JeramayaGramby/AnalogStateBuckConverter/cad/step/BLOCK_10/SMF5_0A.step

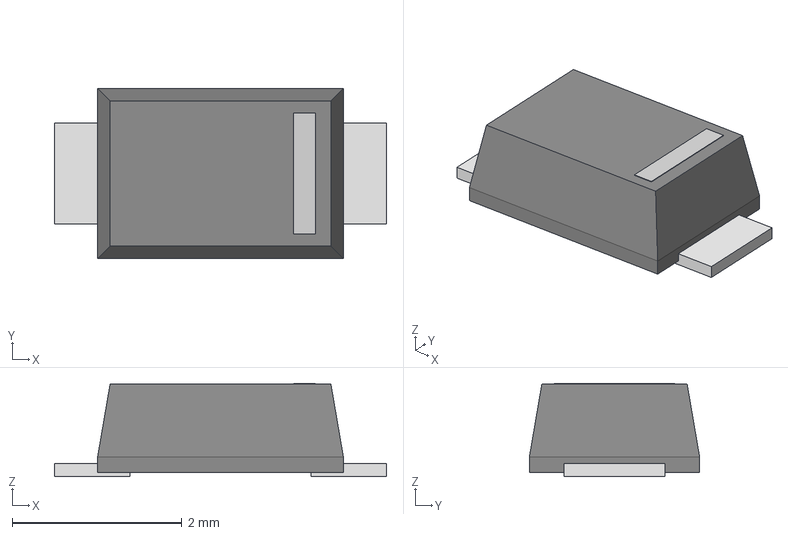
[picture p15: CAD file, 2026-02-01]
cad/step/BLOCK_10/SMF5_0A.step
3.91 x 2.01 x 1.10 mm
