JeramayaGramby/AnalogStateBuckConverter/cad/step/BLOCK_3/NPNTRANSISTOR.step

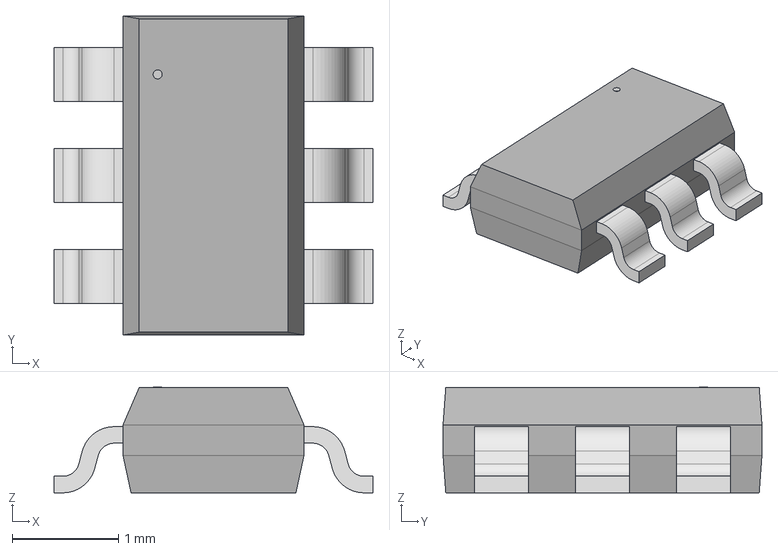
[picture p16: CAD file, 2026-01-31]
cad/step/BLOCK_3/NPNTRANSISTOR.step
3.00 x 3.00 x 0.993 mm
