JeramayaGramby/AnalogStateBuckConverter/cad/step/BLOCK_4/TNPV1206330KBYEA.step

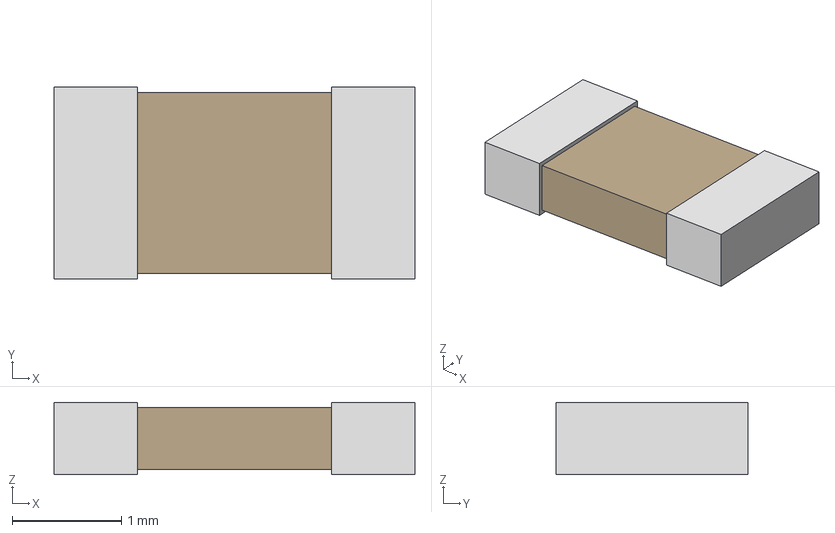
[picture p17: CAD file, 2026-01-31]
cad/step/BLOCK_4/TNPV1206330KBYEA.step
3.30 x 1.75 x 0.66 mm
