JeramayaGramby/AnalogStateBuckConverter/cad/step/BLOCK_5/CRCW040256K2FKED.STEP

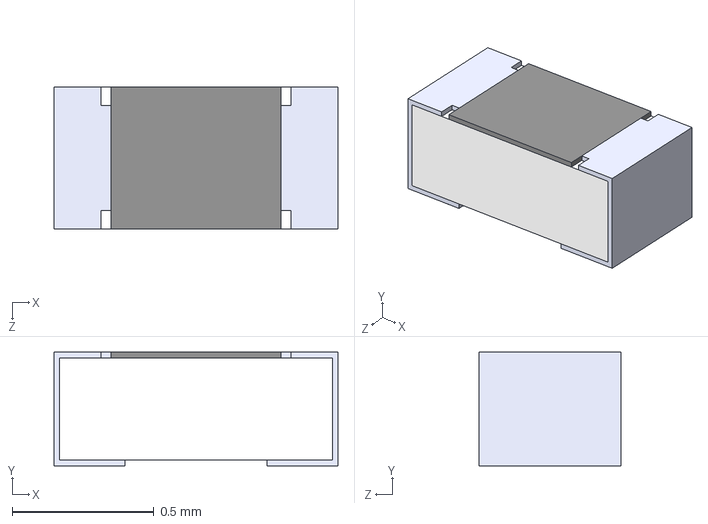
[picture p18: CAD file, 2026-01-31]
cad/step/BLOCK_5/CRCW040256K2FKED.STEP
1 x 0.4 x 0.5 mm
