JeramayaGramby/AnalogStateBuckConverter/cad/step/BLOCK_6/600S100JT250XT4K.step

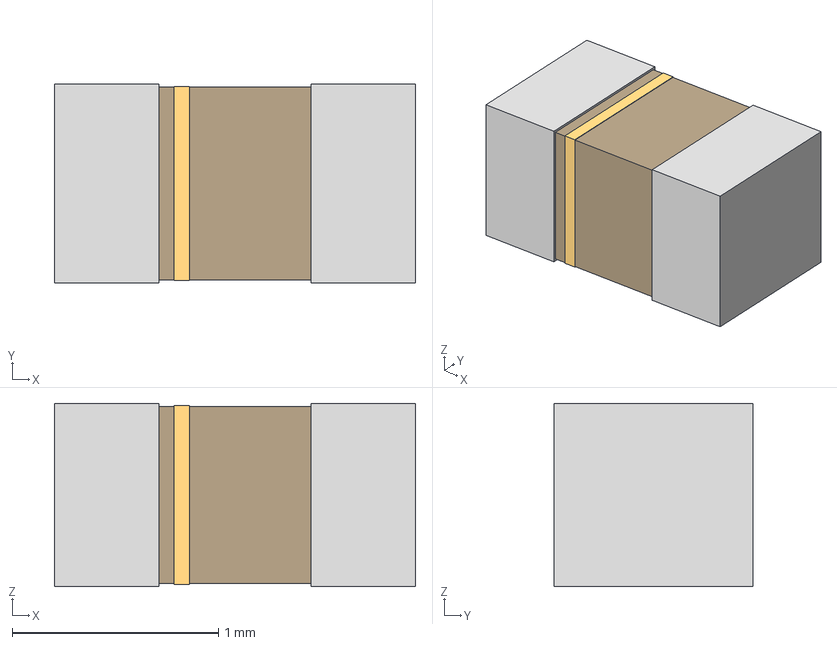
[picture p19: CAD file, 2026-01-31]
cad/step/BLOCK_6/600S100JT250XT4K.step
1.75 x 0.966 x 0.889 mm
