JeramayaGramby/AnalogStateBuckConverter/cad/step/BLOCK_7/CRCW06031K20FKEA.step

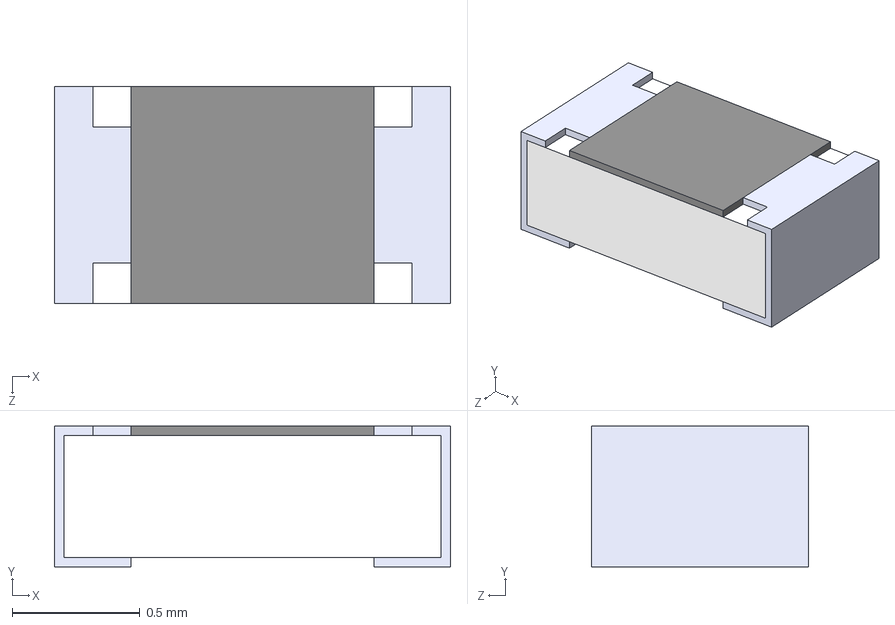
[picture p20: CAD file, 2026-01-31]
cad/step/BLOCK_7/CRCW06031K20FKEA.step
1.55 x 0.55 x 0.85 mm
