JeramayaGramby/AnalogStateBuckConverter/cad/step/BLOCK_1/EDK476M050S9HAA.step

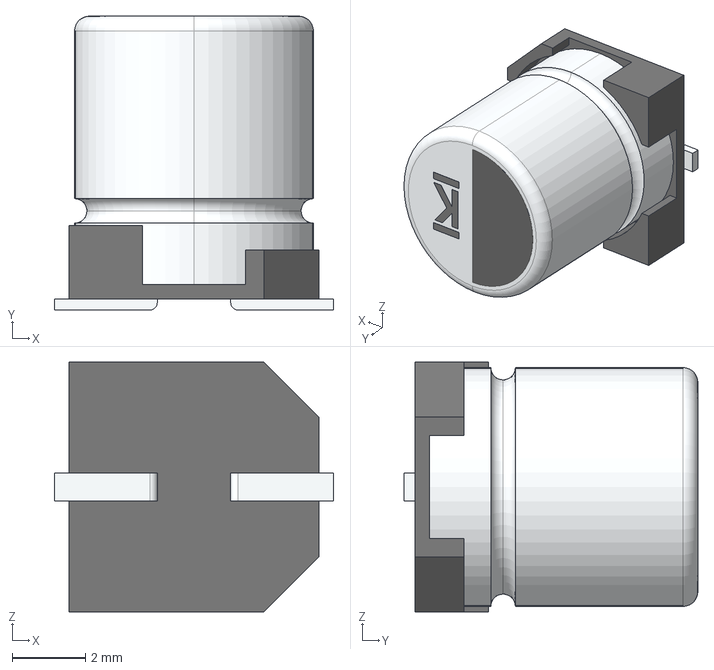
[picture p21: CAD file, 2026-01-30]
cad/step/BLOCK_1/EDK476M050S9HAA.step
7.60 x 8.01 x 6.80 mm
