JeramayaGramby/AnalogStateBuckConverter/cad/step/BLOCK_10/VJ0603Y105KXJCW1BC.step

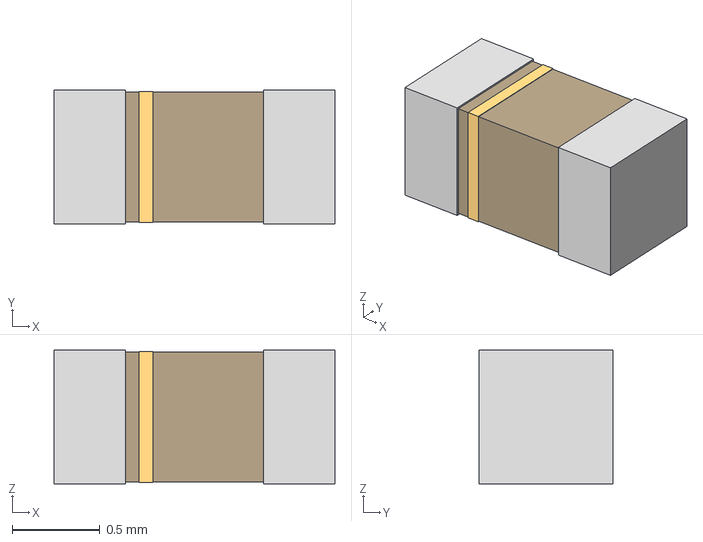
[picture p22: CAD file, 2026-01-31]
cad/step/BLOCK_10/VJ0603Y105KXJCW1BC.step
1.60 x 0.762 x 0.762 mm
