JeramayaGramby/AnalogStateBuckConverter/cad/step/BLOCK_3/PCHANNEL.step

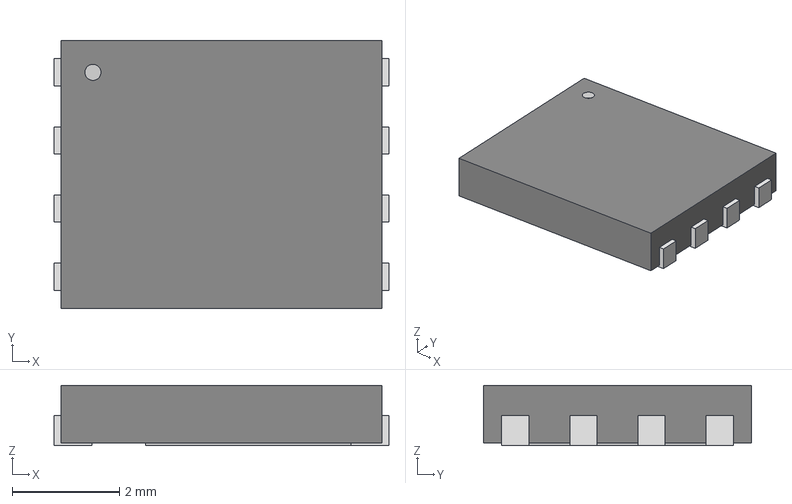
[picture p23: CAD file, 2026-01-31]
cad/step/BLOCK_3/PCHANNEL.step
6.25 x 5.00 x 1.12 mm
