JeramayaGramby/AnalogStateBuckConverter/cad/step/BLOCK_4/CRCW060310K0FKEA.step

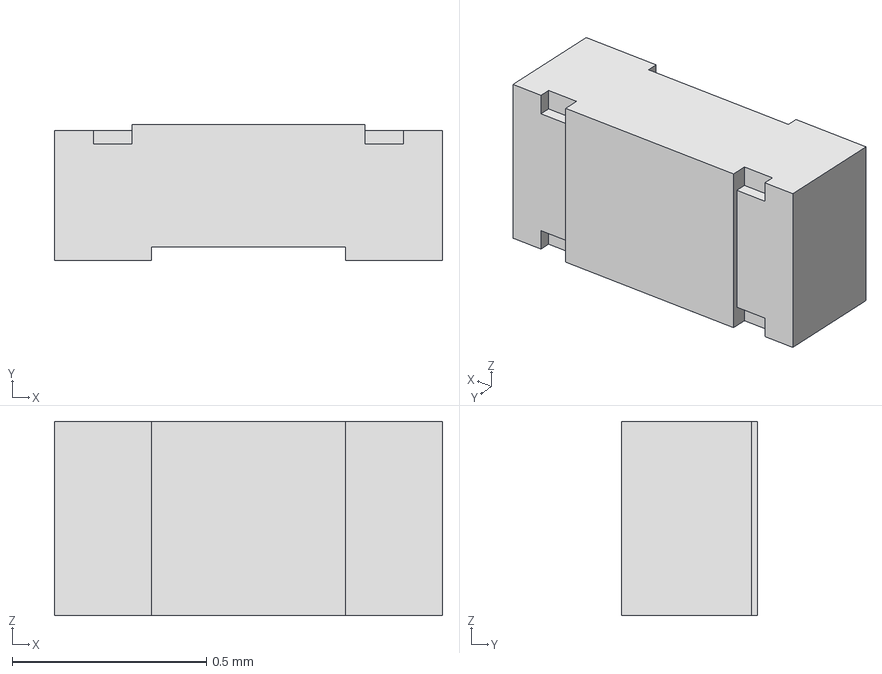
[picture p24: CAD file, 2026-01-31]
cad/step/BLOCK_4/CRCW060310K0FKEA.step
1.00 x 0.35 x 0.5 mm
