JeramayaGramby/AnalogStateBuckConverter/cad/step/BLOCK_5/A768EB226M1HLAE048.step

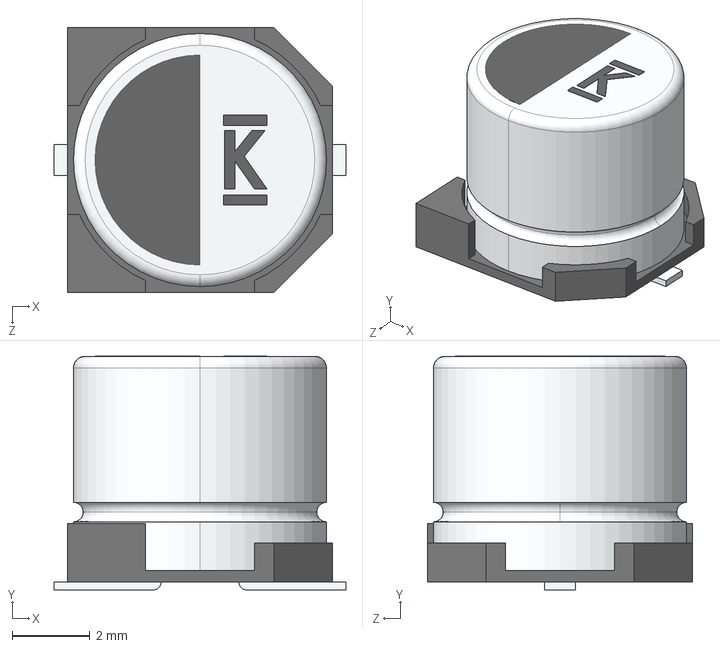
[picture p25: CAD file, 2026-01-31]
cad/step/BLOCK_5/A768EB226M1HLAE048.step
7.50 x 6.00 x 6.80 mm
