JeramayaGramby/AnalogStateBuckConverter/cad/step/BLOCK_1/FUSE_0PTF0078P_LTF.step

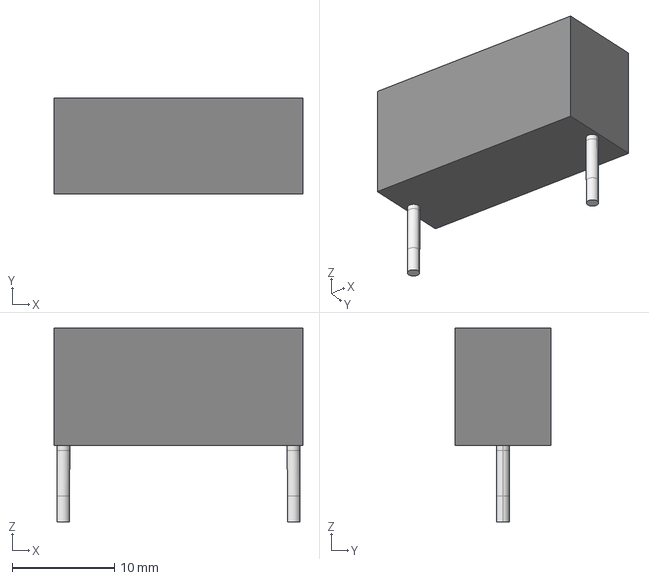
[picture p26: CAD file, 2026-01-30]
cad/step/BLOCK_1/FUSE_0PTF0078P_LTF.step
24.4 x 9.40 x 19.0 mm
