JeramayaGramby/AnalogStateBuckConverter/cad/step/BLOCK_10/C0603C104K5RAC7867.step

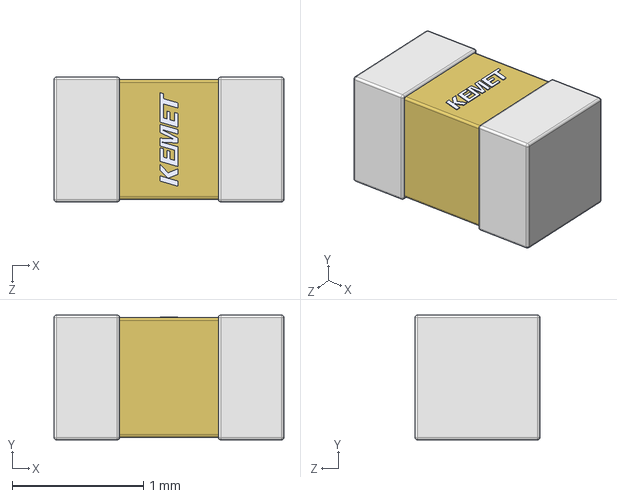
[picture p27: CAD file, 2026-01-30]
cad/step/BLOCK_10/C0603C104K5RAC7867.step
1.75 x 0.95 x 0.95 mm
