JeramayaGramby/AnalogStateBuckConverter/cad/step/BLOCK_1/Same_Sky_PJ-063AH.step

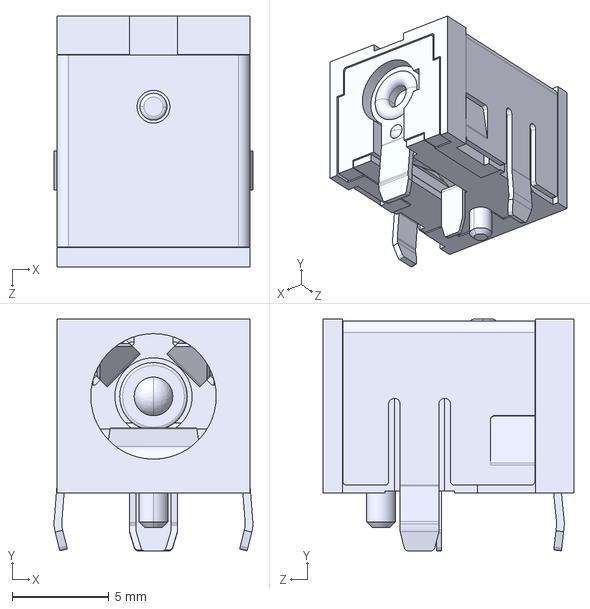
[picture p28: CAD file, 2026-01-30]
cad/step/BLOCK_1/Same_Sky_PJ-063AH.step
10.3 x 12.0 x 13.0 mm
