JeramayaGramby/AnalogStateBuckConverter/cad/step/BLOCK_1/FUSE_0239003_MXP_LTF.step

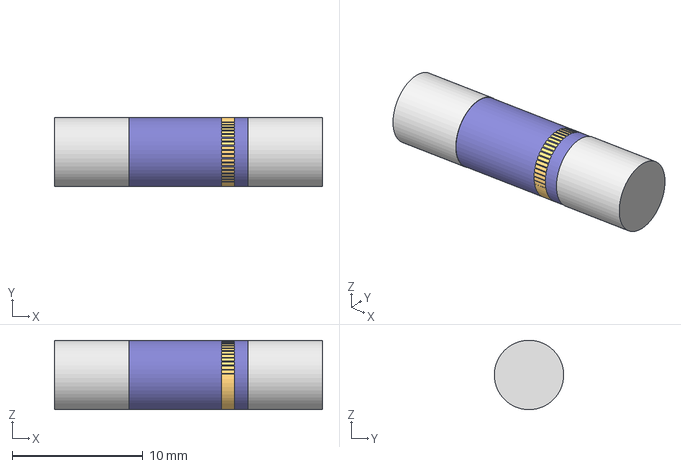
[picture p29: CAD file, 2026-01-30]
cad/step/BLOCK_1/FUSE_0239003_MXP_LTF.step
20.5 x 5.31 x 5.30 mm
