JeramayaGramby/AnalogStateBuckConverter/cad/step/BLOCK_1/SBR3U60P1Q-13.stp

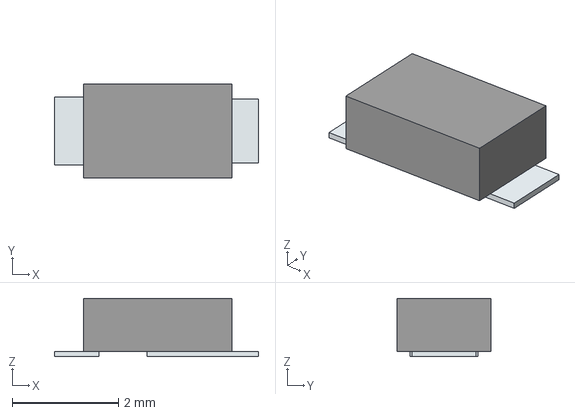
[picture p30: CAD file, 2026-01-30]
cad/step/BLOCK_1/SBR3U60P1Q-13.stp
3.84 x 1.78 x 1.10 mm
Pins
